Marcus10110/DelSolClock/firmware/src/quarter_mile.cpp

#include "quarter_mile.h"
#include "quarter_mile_screens.h"
#include "simple_screens.h"
#include "tft.h"
#include "motion.h"

#include <TinyGPSPlus.h>

#include <algorithm>
#include <optional>

namespace QuarterMile
{
    enum class QuarterMileState
    {
        Start,
        Launch,
        InProgress,
        Summary,
    };
    namespace
    {
        QuarterMileState mState{ QuarterMileState::Start };

        struct Location
        {
            double mLatitude{ 0 };
            double mLongitude{ 0 };
        };

        std::optional<Location> mStartLocation;
        uint32_t mStartTimeMs{ 0 };
        display::quarter_mile::SummaryProps gSummary;
    }

    void Reset()
    {
        mState = QuarterMileState::Start;
        mStartLocation = std::nullopt;
        mStartTimeMs = 0;
        gSummary = display::quarter_mile::SummaryProps();
    }

    void Service( GFXcanvas16* display, Tft::Tft* tft, CarIO::ButtonEvents button_events, TinyGPSPlus* gps )
    {
        // we'll probably draw the screen from here.
        if( mState == QuarterMileState::Start )
        {
            auto motion = Motion::GetState();
            if( !motion.mCalibrated )
            {
                if( button_events.mMinuteButtonPressed )
                {
                    Motion::Calibrate();
                }

                display::DrawCalibrationMissing( display );
                tft->DrawCanvas( display );
                return;
            }

            display::quarter_mile::DrawStart( display );
            tft->DrawCanvas( display );

            if( button_events.mMinuteButtonPressed )
            {
                mState = QuarterMileState::Launch;
            }
        }
        else if( mState == QuarterMileState::Launch )
        {
            auto motion = Motion::GetState();
            display::quarter_mile::LaunchProps launch;
            launch.accelerationG = motion.mForward;
            display::quarter_mile::DrawLaunch( display, launch );
            tft->DrawCanvas( display );
            // wait for some g threshold to detect launch.
            // note, we need forward direction specifically!
            // for now, just press the minute button to simulate launch.


            if( motion.mForward >= 0.2 || button_events.mMinuteButtonPressed )
            {
                mState = QuarterMileState::InProgress;
                mStartTimeMs = millis();
                if( gps->location.isValid() )
                {
                    // store the start location.
                    mStartLocation = Location{ gps->location.lat(), gps->location.lng() };
                }
            }
        }
        else if( mState == QuarterMileState::InProgress )
        {
            auto elapsed_ms = millis() - mStartTimeMs;
            auto acceleration = Motion::GetState();
            double distance_miles = 0;
            if( mStartLocation.has_value() && gps->location.isValid() )
            {
                distance_miles = TinyGPSPlus::distanceBetween( mStartLocation->mLatitude, mStartLocation->mLongitude, gps->location.lat(),
                                                               gps->location.lng() ) *
                                 0.000621371;
            }
            display::quarter_mile::InProgressProps in_progress;
            in_progress.timeSec = elapsed_ms / 1000.0;

            in_progress.accelerationG = acceleration.mForward;
            in_progress.distanceMiles = distance_miles;
            in_progress.speedMph = gps->speed.isValid() ? gps->speed.mph() : 0;

            gSummary.maxAccelerationG = std::max( gSummary.maxAccelerationG, in_progress.accelerationG );
            gSummary.maxSpeedMph = std::max( gSummary.maxSpeedMph, in_progress.speedMph );

            if( gSummary.zeroSixtyTimeSec == 0 && in_progress.speedMph >= 60.0 )
            {
                gSummary.zeroSixtyTimeSec = in_progress.timeSec;
            }

            display::quarter_mile::DrawInProgress( display, in_progress );
            tft->DrawCanvas( display );

            if( distance_miles >= 0.25 )
            {
                gSummary.quarterMileTimeSec = in_progress.timeSec;
                mState = QuarterMileState::Summary;
            }

            // press M to cancel.
            if( button_events.mMinuteButtonPressed )
            {
                Reset();
            }
        }
        else if( mState == QuarterMileState::Summary )
        {
            display::quarter_mile::DrawSummary( display, gSummary );
            tft->DrawCanvas( display );

            // pressing M will start over. press H to exit.
            if( button_events.mMinuteButtonPressed )
            {
                Reset();
            }
        }
    }
}
