Marcus10110/DelSolClock/firmware/include/debug_service.h

#pragma once

class BLEServer;
// The debug service allows connected BLE devices to check for and download ESP32 crash dumps from flash.
namespace DebugService
{
    bool StartDebugService( BLEServer* server );
    void HandleAssertCase();
}
